sampan2000/FFB_Base_vs_Robs03/img/IMG_20241018_195518.jpg

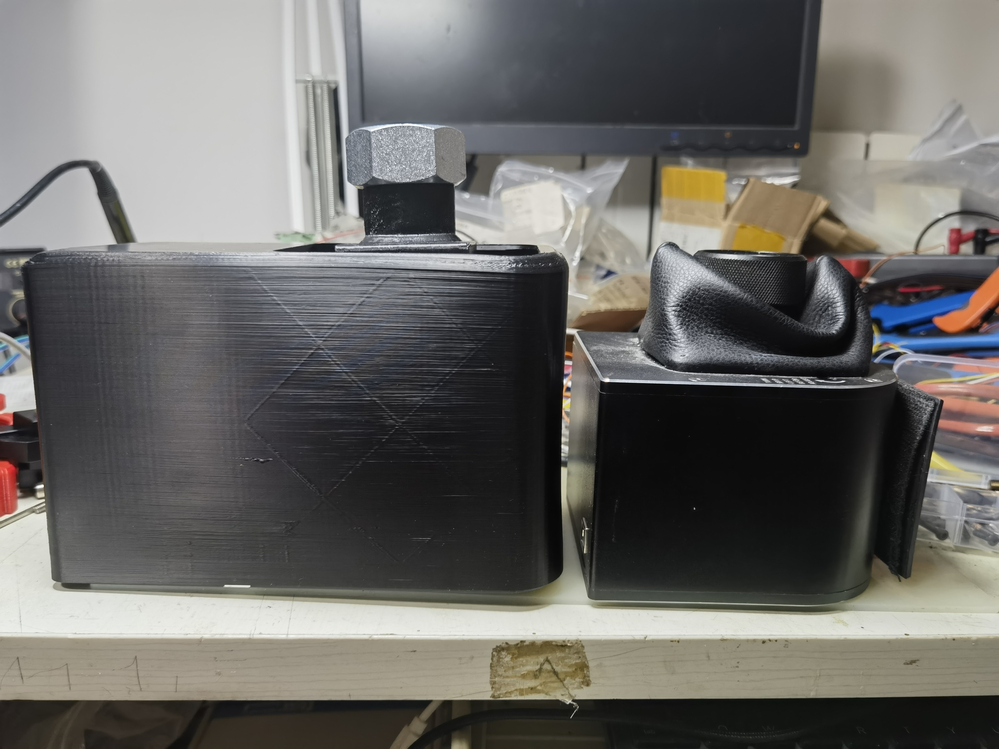
img/IMG_20241018_195518.jpg
