sampan2000/FFB_Base_vs_Robs03/stl/治具2.jpg

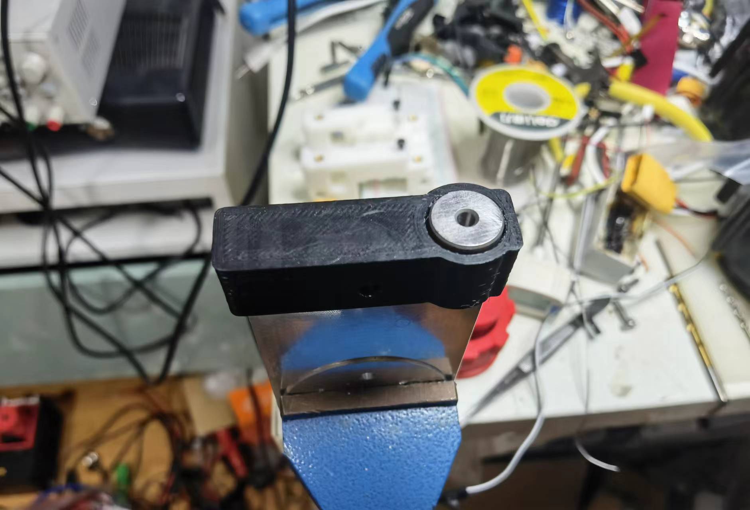
stl/治具2.jpg
